sparkfun/SparkFun_Qwiic_Hall_Effect_Sensor_TMAG5273/docs/assets/img/hookup_guide/23880-bottom.png

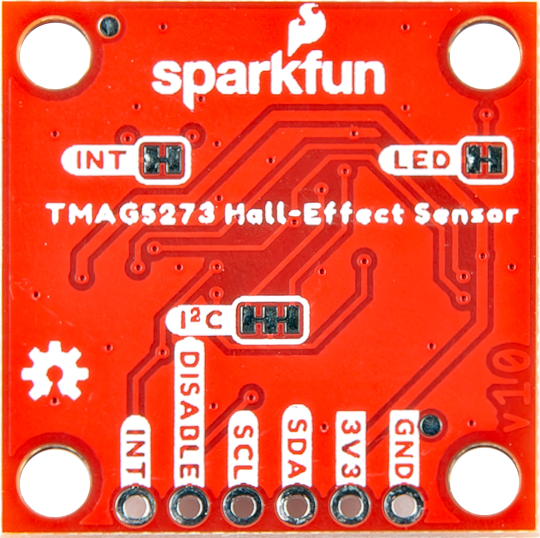
docs/assets/img/hookup_guide/23880-bottom.png
