sparkfun/SparkFun_Qwiic_Hall_Effect_Sensor_TMAG5273/docs/assets/img/hookup_guide/23881-template.png

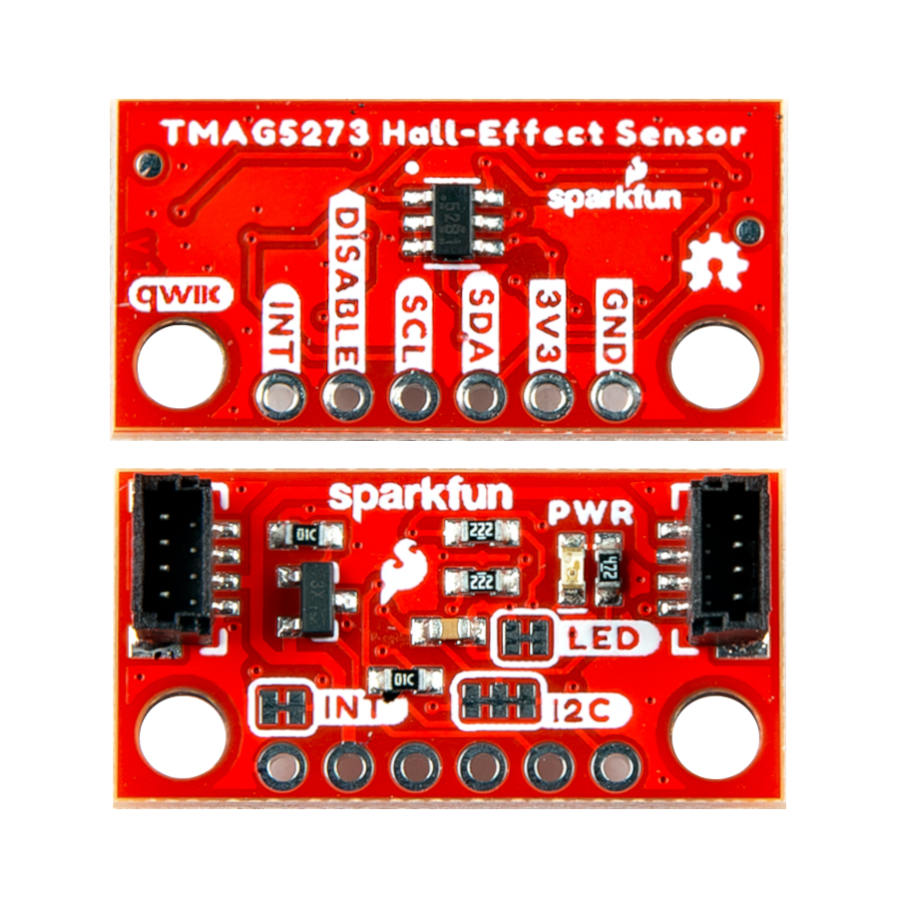
docs/assets/img/hookup_guide/23881-template.png
