sparkfun/SparkFun_Qwiic_Hall_Effect_Sensor_TMAG5273/docs/assets/img/hookup_guide/back_power.png

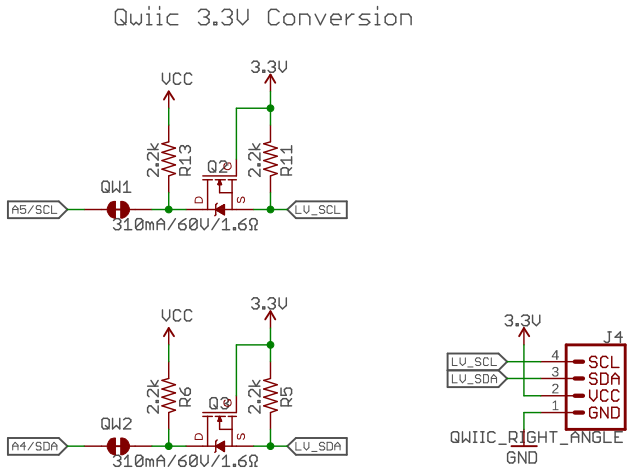
docs/assets/img/hookup_guide/back_power.png
