sparkfun/SparkFun_Qwiic_Hall_Effect_Sensor_TMAG5273/docs/assets/img/hookup_guide/example-power-disable.jpg

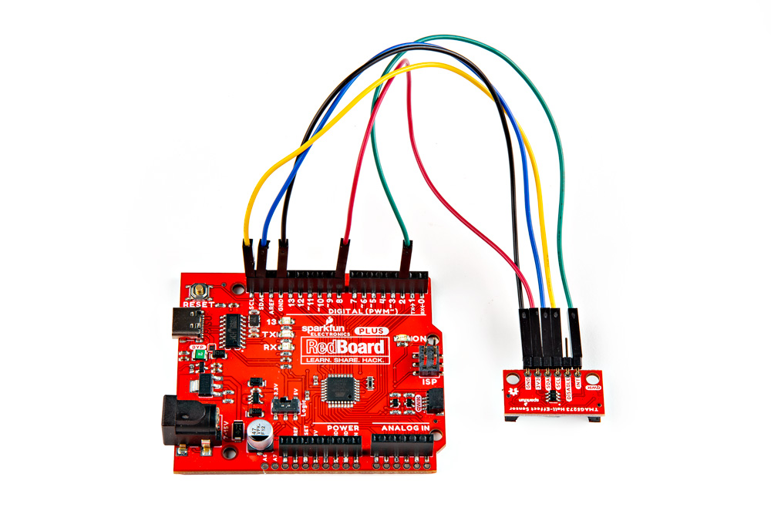
docs/assets/img/hookup_guide/example-power-disable.jpg
