sparkfun/SparkFun_Qwiic_Hall_Effect_Sensor_TMAG5273/docs/assets/img/hookup_guide/TMAG5273-1x1.png

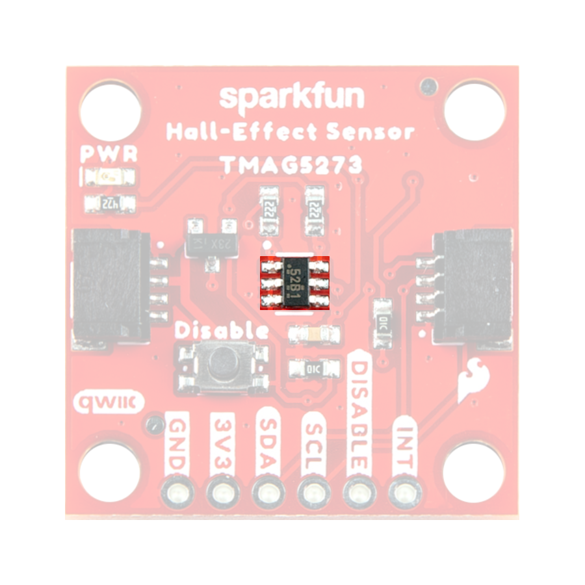
docs/assets/img/hookup_guide/TMAG5273-1x1.png
