sparkfun/SparkFun_Qwiic_Hall_Effect_Sensor_TMAG5273/docs/assets/board_files/dimensions-1x1.pdf

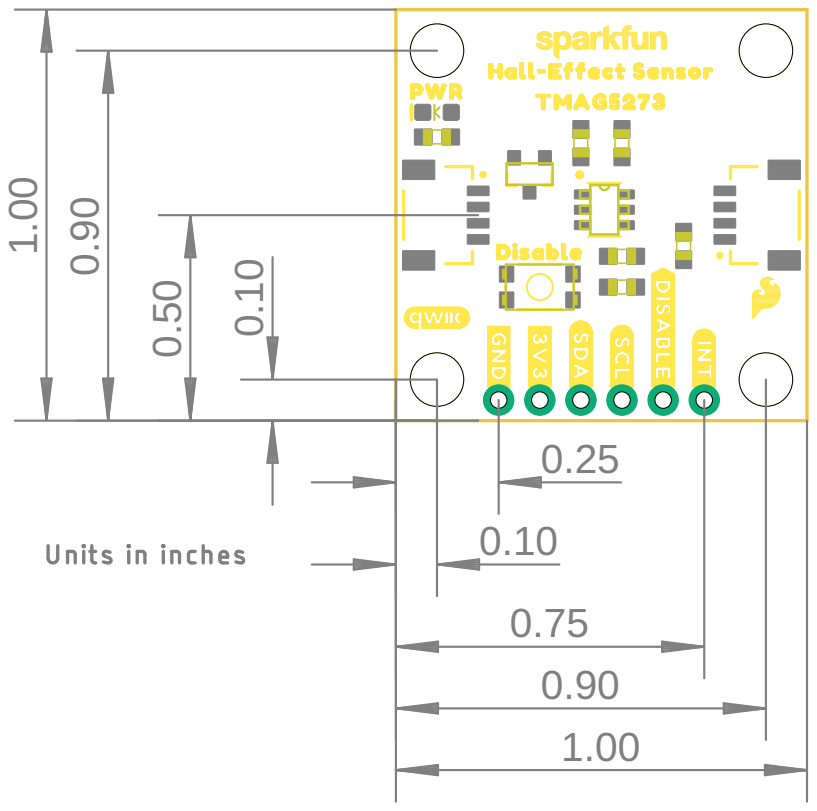
[picture p68: page 1]
