sparkfun/SparkFun_Qwiic_Hall_Effect_Sensor_TMAG5273/docs/assets/board_files/dimensions-mini.pdf

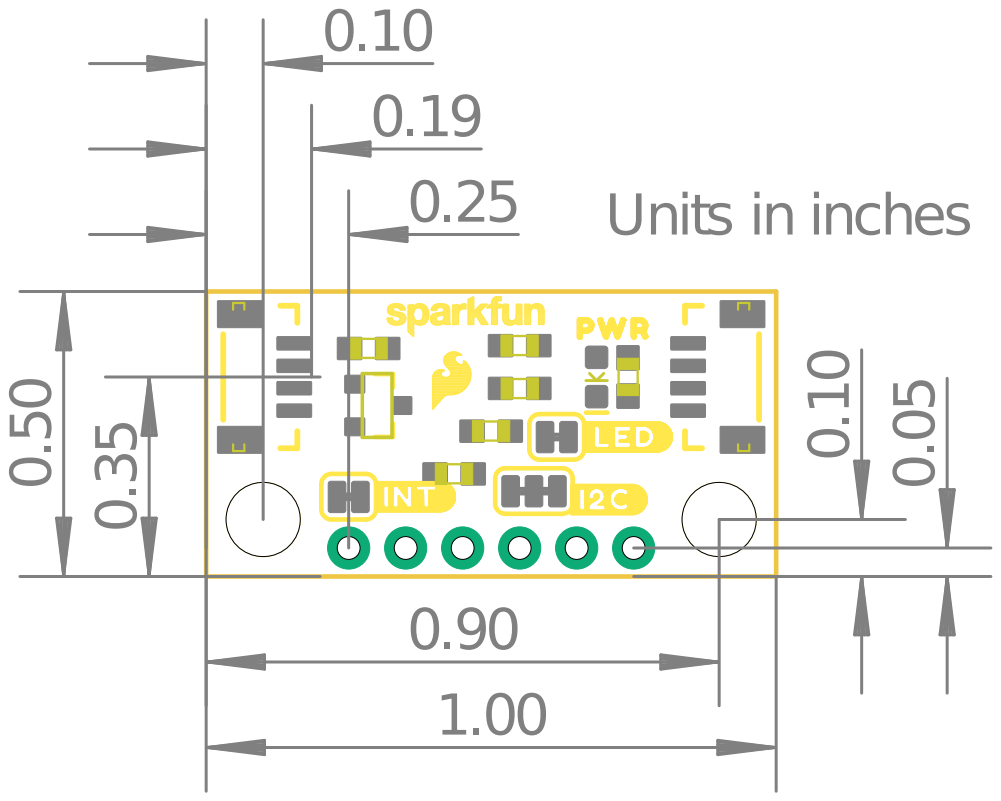
[picture p69: page 1]

Units in inches
