sparkfun/SparkFun_Qwiic_Hall_Effect_Sensor_TMAG5273/docs/assets/board_files/sensor_position-1x1.pdf

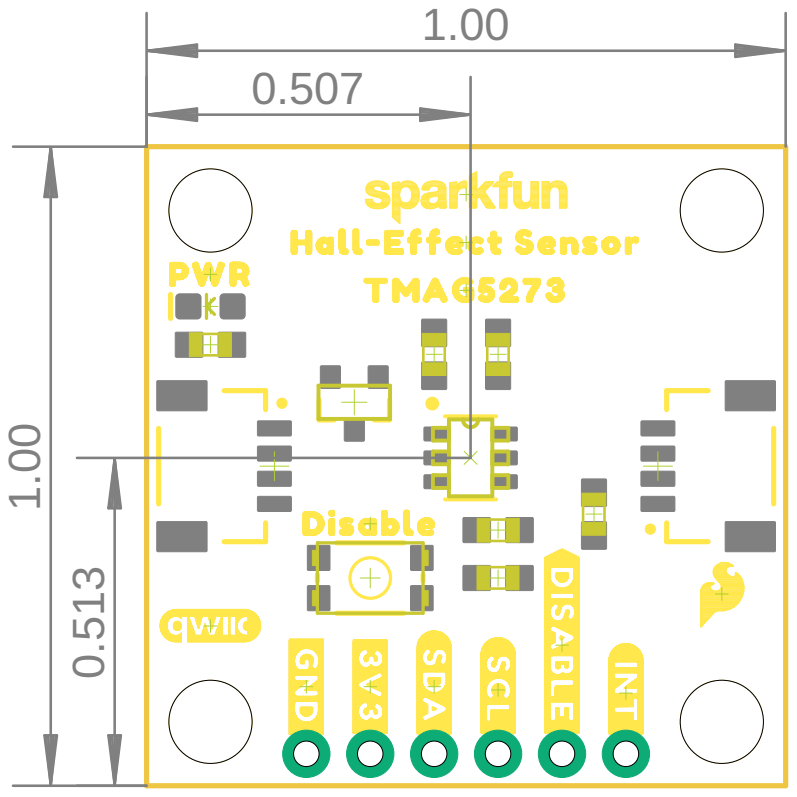
[picture p70: page 1]
