sparkfun/SparkFun_Qwiic_Hall_Effect_Sensor_TMAG5273/docs/assets/board_files/sensor_position-mini.pdf

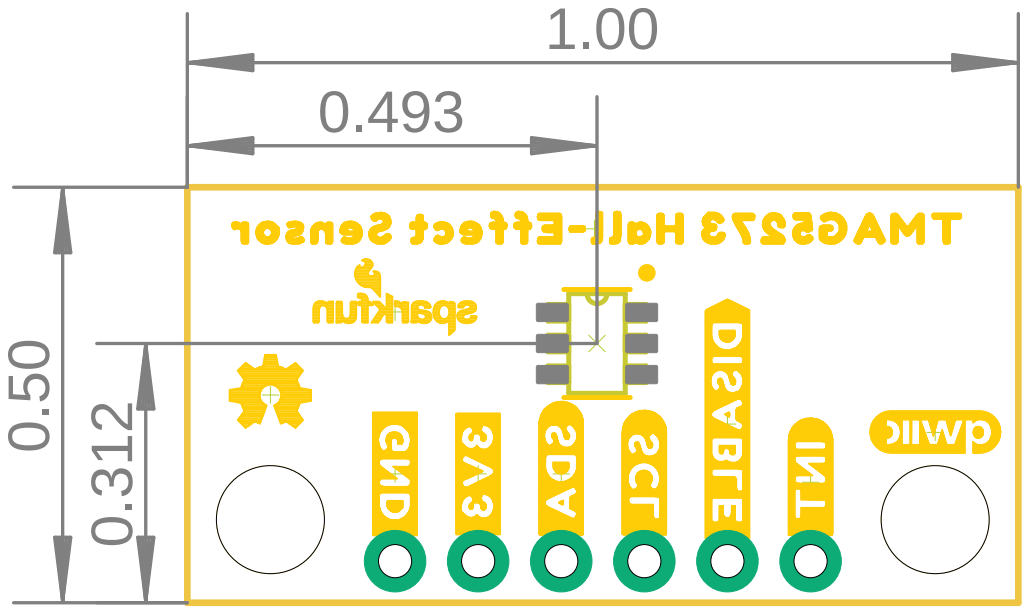
[picture p71: page 1]
